PapaSierra555/M2-Community-Node/meshtastic/pdf/CCC26_DeviceCard_Back.pdf

# CCC26

## MESH DEVICE

01

CCC26 — M2 Community Node — Off-Grid Event Communications Return to operator after event

# CCC26

## MESH DEVICE

02

CCC26 — M2 Community Node — Off-Grid Event Communications Return to operator after event

# CCC26

## MESH DEVICE

03

CCC26 — M2 Community Node — Off-Grid Event Communications Return to operator after event

# CCC26

## MESH DEVICE

04

CCC26 — M2 Community Node — Off-Grid Event Communications Return to operator after event

# CCC26

## MESH DEVICE

05

CCC26 — M2 Community Node — Off-Grid Event Communications Return to operator after event

# CCC26

## MESH DEVICE

06

CCC26 — M2 Community Node — Off-Grid Event Communications Return to operator after event

# CCC26

## MESH DEVICE

07

CCC26 — M2 Community Node — Off-Grid Event Communications Return to operator after event

# CCC26

## MESH DEVICE

08

CCC26 — M2 Community Node — Off-Grid Event Communications Return to operator after event

# CCC26

## MESH DEVICE

PS-01

CCC26 — M2 Community Node — Off-Grid Event Communications Return to operator after event

# CCC26

## MESH DEVICE

PS-02

CCC26 — M2 Community Node — Off-Grid Event Communications Return to operator after event

# CCC26

## MESH DEVICE

PS-03

CCC26 — M2 Community Node — Off-Grid Event Communications Return to operator after event
