PapaSierra555/M2-Community-Node/community-outreach/meshtastic-onesheet/ccc_meshtastic_onesheet.pdf

# M2 Community Node

C A R O L I N A C A P A B I L I T I E S C O - O P | • | L F H I

# MESHTASTIC FIELD GUIDE

R A D I O M E S H C O M M U N I C AT I O N S

## WHAT IS MESHTASTIC?

Meshtastic turns a small handheld radio into a private group

messaging device — no cell service, no WiFi, no internet required.

The radio pairs to a free app on your phone over Bluetooth.

Everyone on the same network can send and receive text

messages, and the network stays up even when all other

communications fail.

At an M2 Node deployment, Meshtastic extends your radio reach

beyond the node's WiFi footprint. Learn more at meshtastic.org.

WHY MESHTASTIC FOR COMMUNITY PREPAREDNESS?

Meshtastic is free, open-source, and completely off-grid. Radios

communicate directly with each other — no phone company, no

server, no single point of failure. A small group of 3–5 radios can

cover a neighborhood, an event site, or a deployment area with no

infrastructure at all.

HOW CAN I GET STARTED?

At any M2 Node activation, Meshtastic radios will be on the

network. Install the free app, ask the network operator to add you

to the active channel, and you're live. If you'd like your own radio for

future deployments, see the options to the right.

Field note: Use a dedicated or secondary device when possible — an

old phone with no SIM card works perfectly. Keep your primary

device available for other mission needs.

SECURITY & OPERATIONAL TIPS

## APP DOWNLOAD

Download the free Meshtastic app for your phone. Scan the QR code or

search Meshtastic in your app store.

Android App (https://play.google.com/store/apps/details?id=com.geeksville.mesh)

Google Play Store

play.google.com (https://play.google.com/store/apps/details?id=com.geeksville.mesh)

iPhone App (https://apps.apple.com/us/app/meshtastic/id1586432531)

Apple App Store

apps.apple.com (https://apps.apple.com/us/app/meshtastic/id1586432531)

## HARDWARE OPTIONS

Most devices are ready to use out of the box. Prices listed are

approximate.

$40

SenseCAP T1000-E (https://www.seeedstudio.com/SenseCAP-Card-Tracker-T1000-E-for-Meshtastic-p-5913.html)

H E LT E C T 1 1 4 — T W O O P T I O N S

$43 Heltec T114 (Rokland) (https://store.rokland.com/products/heltec-mesh-node-t114-with-optional-1-14-inch-tft-display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)

$50

Heltec T114 Kit (Amazon) (https://www.amazon.com/Heltec-Meshtastic-T114-Crabiner-Bluetooth/dp/B0F3X3WNJP)

$53 LILYGO T-Echo (https://lilygo.cc/products/t-echo-meshtastic)

L I LYG O T- D E C K — N O P H O N E N E E D E D

A fully self-contained device with built-in keyboard and screen — no phone required.

Often out of stock in the US; check before ordering.

Q | W | E | R | T | Y | IU | PO
A | S | D | F | G | H | KJ | L
alt | Z | X | C | V | B | MN
$82 | LILYGO T-Deck Plus (https://lilygo.cc/products/t-deck-plus-meshtastic?variant=51953085382837)

Full hardware list: meshtastic.org/docs/hardware

M2 COMMUNITY NODE

carolinacapabilitiesco-op.com • lightfighterhomefront.org

Device illustrations © Meshtastic Project, (https://github.com/meshtastic/meshtastic) Apache 2.0

meshtastic.org • Open Source • CC BY-NC-SA 4.0

No cell network or internet required — radios talk directly to each

other, up to several kilometers range depending on terrain.

—

Turn on Airplane Mode, then re-enable Bluetooth only. Your phone

connects to the radio and nothing else.

—

An old phone or tablet with no SIM card works perfectly. No carrier

plan needed.

—

- Credit card size — easy to carry or clip to gear
- Includes GPS location tracking
- Board only — you supply a battery and case
- Many free 3D-printable case designs available
- Best battery life — good for extended field use
- Battery, case, and GPS included — snap together, no soldering
- Ready to use out of the box — GPS included, no assembly
- Ships from US or China warehouses
- Docs: meshtastic.org/docs/…/tdeck (https://meshtastic.org/docs/hardware/devices/lilygo/tdeck/)
