PapaSierra555/M2-Community-Node/community-outreach/pdf/M2_New_Member_Card.pdf

M2 COMMUNITY NODE | CCC26 LFHI

### Get Connected Now

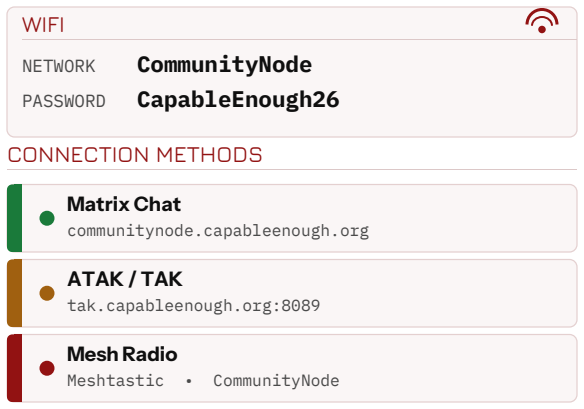
[picture p3: figure]
WIFI; NETWORK; CommunityNode; PASSWORD; CapableEnough26; CONNECTION METHODS; Matrix Chat communitynode.capableenough.org; ATAK / TAK tak.capableenough.org:8089; Mesh Radio Meshtastic • CommunityNode

### WIFI

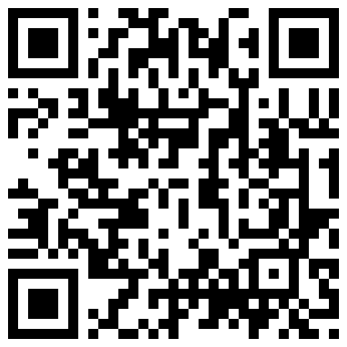
[picture p4: figure]

Scan to join WiFi
CommunityNode • CapableEnough26

Powered by CC BY-NC-SA 4.0 open source hardware & software

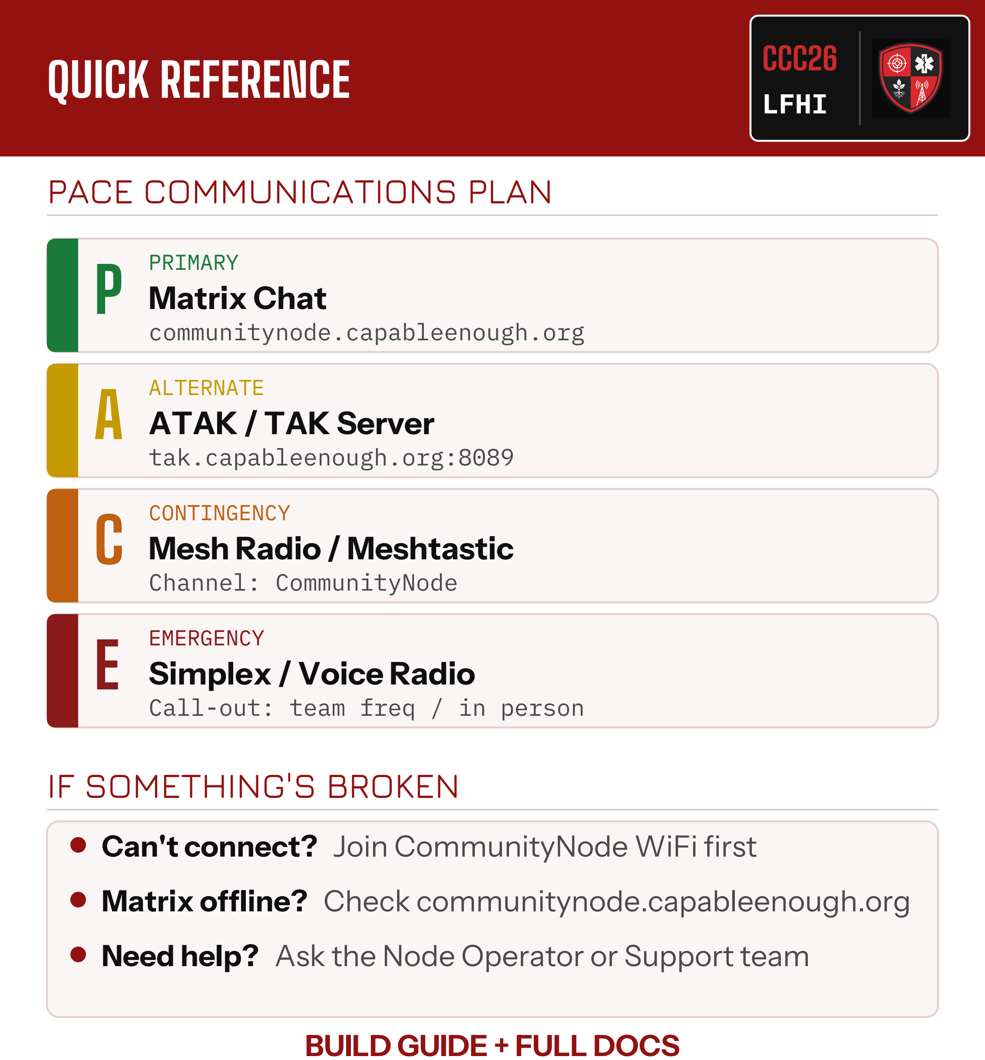
[picture p5: figure]
QUICK REFERENCE; CCC26; LFHI; PACE COMMUNICATIONS PLAN P; PRIMARY Matrix Chat communitynode.capableenough.org; ALTERNATE ATAK / TAK Server tak.capableenough.org:8089; CONTINGENCY Mesh Radio / Meshtastic Channel: CommunityNode; EMERGENCY Simplex / Voice Radio Call-out: team freq / in person; IF SOMETHING'S BROKEN; Matrix offline? Check communitynode.capableenough.org; BUILD GUIDE + FULL DOCS

Can't connect? Join CommunityNode WiFi first

Need help? Ask the Node Operator or Support team

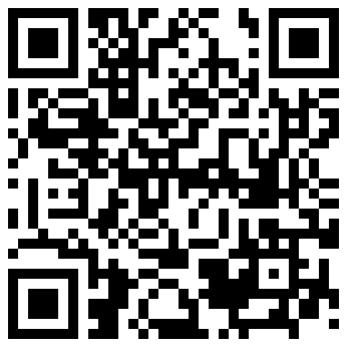
[picture p6: figure]

Bill of materials, configs & step-by-step build guide github.com/PapaSierra555/M2-Community-Node

CC BY-NC-SA 4.0 — Capable Enough Project
