PapaSierra555/M2-Community-Node/community-outreach/pdf/M2_PACE_Card.pdf

# PACE COMMUNICATIONS PLAN

M2 Community Node — Build it. Own it. Control it.

## CCC26

LFHI

A PACE plan defines four tiers of communication, ordered from most capable to most resilient. The M2 Community Node provides all four tiers in a single deployable rack. Each tier operates independently — losing one does not affect the others below it.

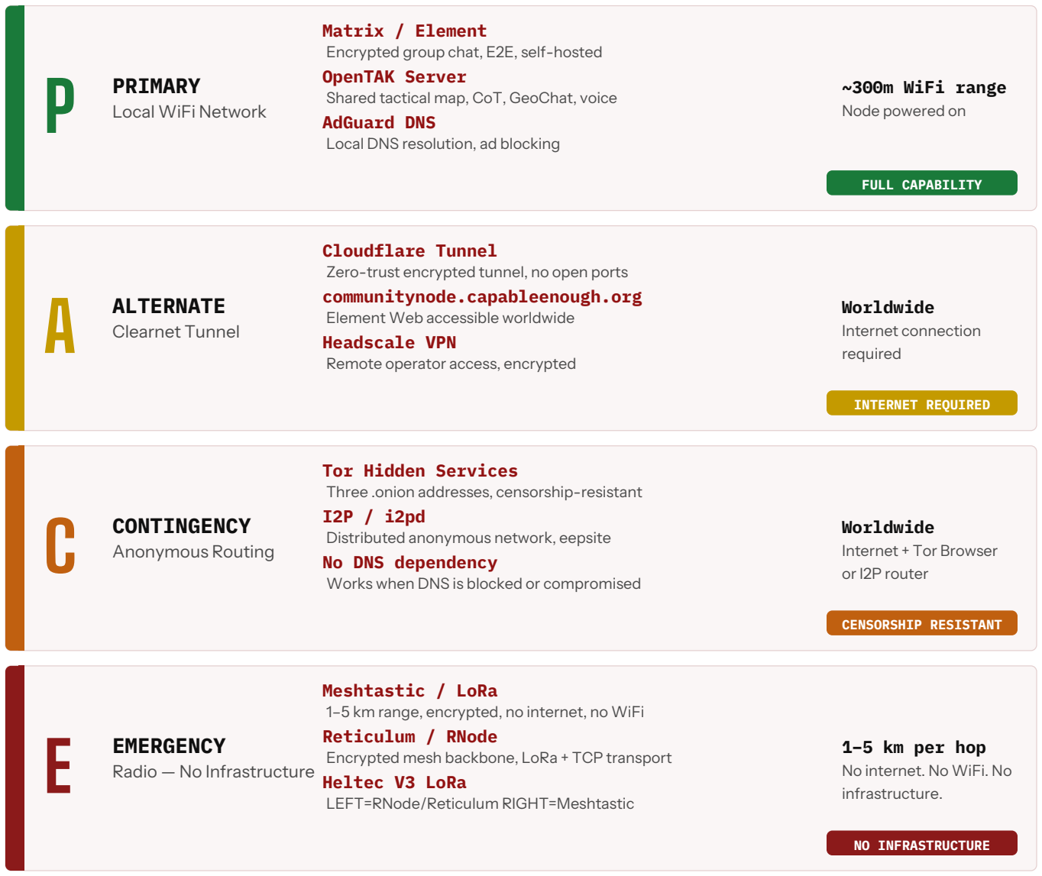
[picture p7: figure]
PRIMARY Local WiFi Network; Matrix / Element Encrypted group chat, E2E, self-hosted OpenTAK Server; AdGuard DNS Local DNS resolution, ad blocking; ~300m WiFi range Node powered on; FULL CAPABILITY; ALTERNATE Clearnet Tunnel; Cloudflare Tunnel; communitynode.capableenough.org Element Web accessible worldwide Headscale VPN Remote operator access, encrypted; Worldwide Internet connection required; INTERNET REQUIRED; CONTINGENCY Anonymous Routing; Tor Hidden Services Three .onion addresses, censorship-resistant I2P / i2pd Distributed anonymous network, eepsite No DNS dependency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

Shared tactical map, CoT, GeoChat, voice

Zero-trust encrypted tunnel, no open ports

Works when DNS is blocked or compromised

1–5 km range, encrypted, no internet, no WiFi

Encrypted mesh backbone, LoRa + TCP transport

## DEPLOYMENT NOTES

Each tier is independent — failure of a higher tier does not affect lower tiers.

Meshtastic and Reticulum operate from the node's onboard LoRa radios — no external hardware needed by operators.

This PACE plan covers the node's output. Operators still need client devices (phone, laptop, ATAK-compatible).

License: CC BY-NC-SA 4.0 — Build one for your community. Cannot be sold. | Capable Enough Project
