PapaSierra555/M2-Community-Node/operational-pdfs/M2_CCC26_Element_JoinCard.pdf

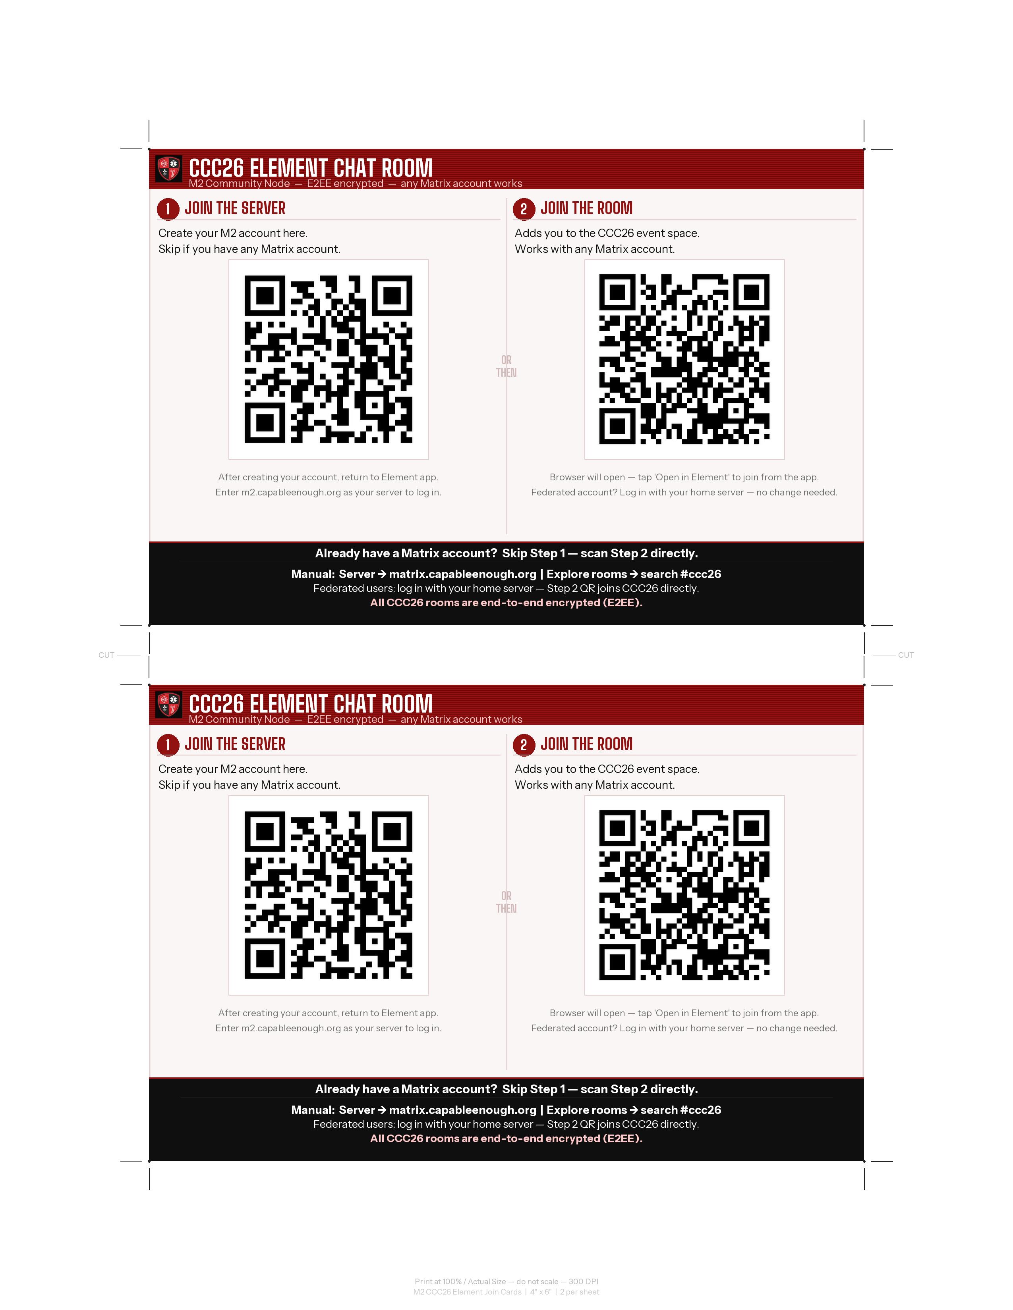
[picture p22: page 1]
