PapaSierra555/M2-Community-Node/operational-pdfs/M2_ATAK_FieldCard.pdf

## ATAK Field Setup

M2 Community Node — Operator Reference

CCC26
LFHI
1. INSTALL APPS
- ATAK-CIV — Play Store (Android only)
- Mumla — Play Store (push-to-talk voice)
- Meshtastic Plugin — GitHub APK (sideload)
2. CONNECT TO SERVER
Option A — Data Package (preferred)
- Join CommunityNode WiFi
- Scan rack QR → tap Open in ATAK Login: field / community
- Tap OK → server connects automatically

Option B — Manual Entry
- Settings > TAK Servers > Add
Server: 192.168.8.20 Port: 8089 (SSL)
- Enroll for cert • uncheck Default SSL
Cert pwd: atakatak
3. SET CALLSIGN
- Settings > My Preferences > Callsign
4. VERIFY
- Your icon appears on the shared map
- Test GeoChat: send a message in #general
CommunityNode WiFi | capableenough.org | v1.0

## Voice & Mesh Setup

M2 Community Node — Operator Reference

CCC26
LFHI

MUMLA — PUSH-TO-TALK VOICE Server: 192.168.8.20
Port: 64738 (no password)
- Open Mumla > Add server > Connect MESHTASTIC — LORA MESH RADIO
- Install Meshtastic app (Play Store)
- Pair Heltec V3 radio via Bluetooth
- ATAK plugin bridges positions + messages TROUBLESHOOTING
- No map tiles? Must be on CommunityNode WiFi
- Can't reach server? Disable VPN, Private DNS, firewall
- Cert error? Delete server, re-add from Step 2
- No GPS? Grant location permission, go outside
- Not on map? Set Reporting Strategy to Consistent
- Still not on map? Toggle server off/on in TAK Servers
- Mumla echo? Use headphones or earbuds
REMOTE ACCESS (OFF-NETWORK)
Web map: tak.capableenough.org
- Email OTP login — browser, full shared map
- Remote ATAK: ask operator for VPN access KEY INFO
Community page: 192.168.8.10:8081
- Element chat: #general on capableenough.org
- Clearnet: element.capableenough.org
- Contact: info@capableenough.org
CommunityNode WiFi | capableenough.org | v1.0
